electronlove/MiniStudio/Neopixel Board.jpg

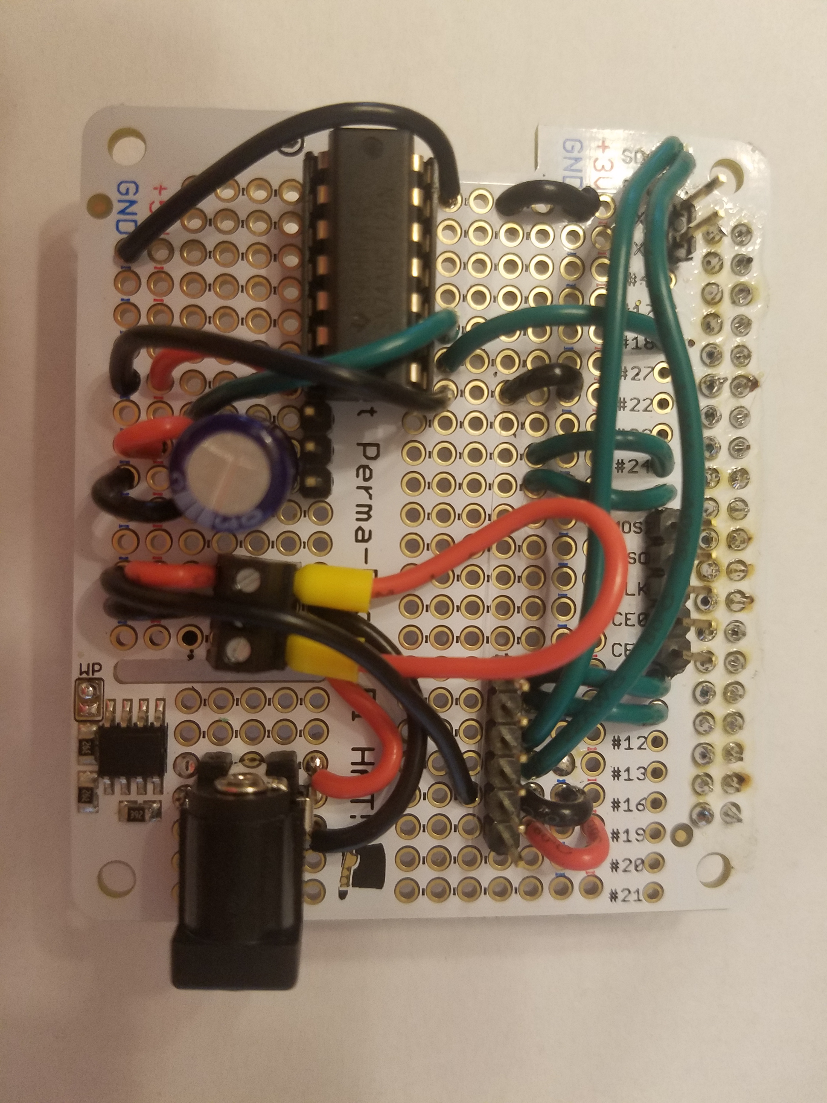
Neopixel Board.jpg
