electronlove/MiniStudio/NeoPixel-Mount.jpg

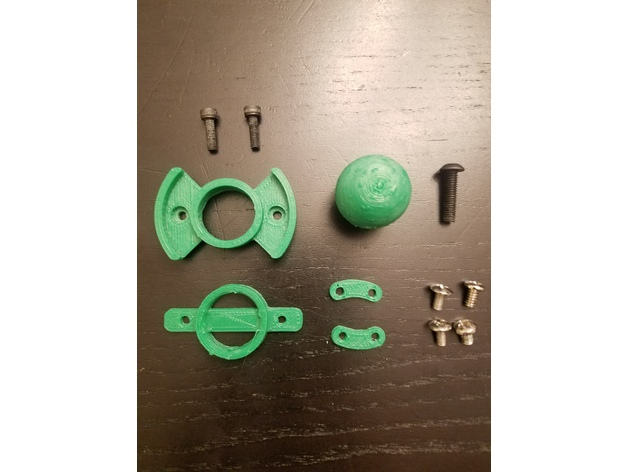
NeoPixel-Mount.jpg
