electronlove/MiniStudio/Snail Box.jpg

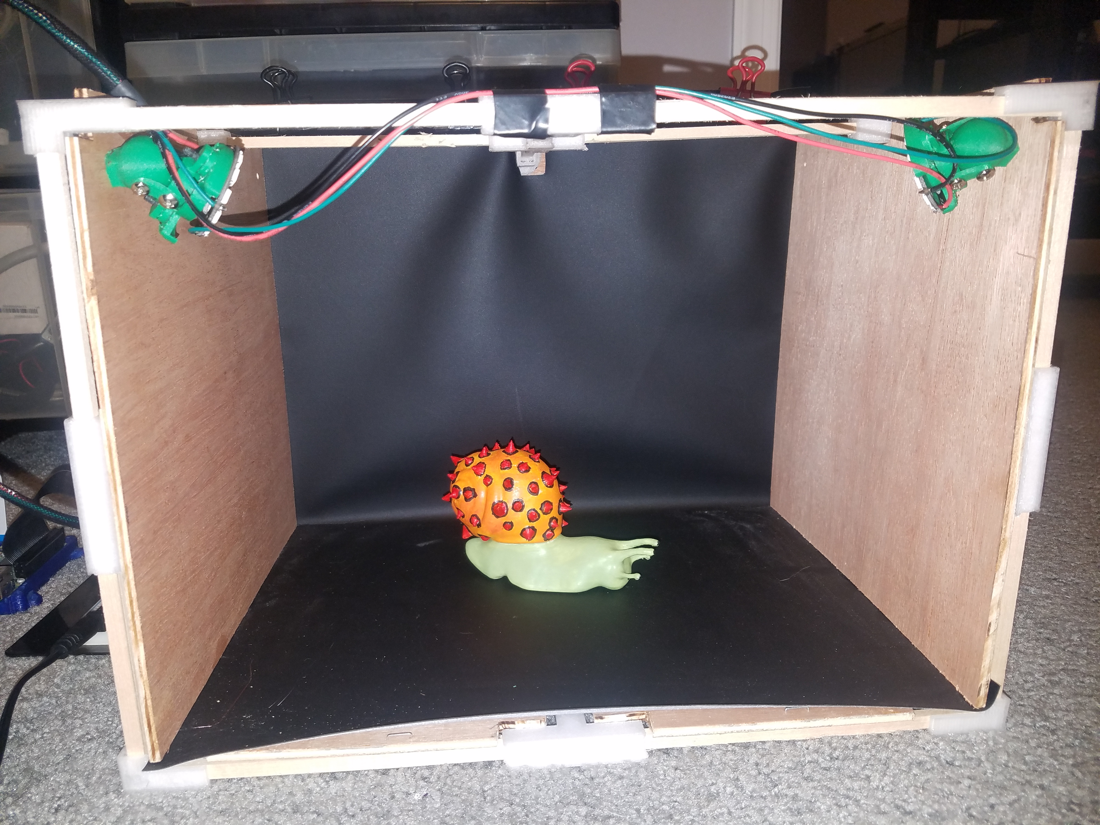
Snail Box.jpg
