electronlove/MiniStudio/STL/LED  with diffuser.jpg

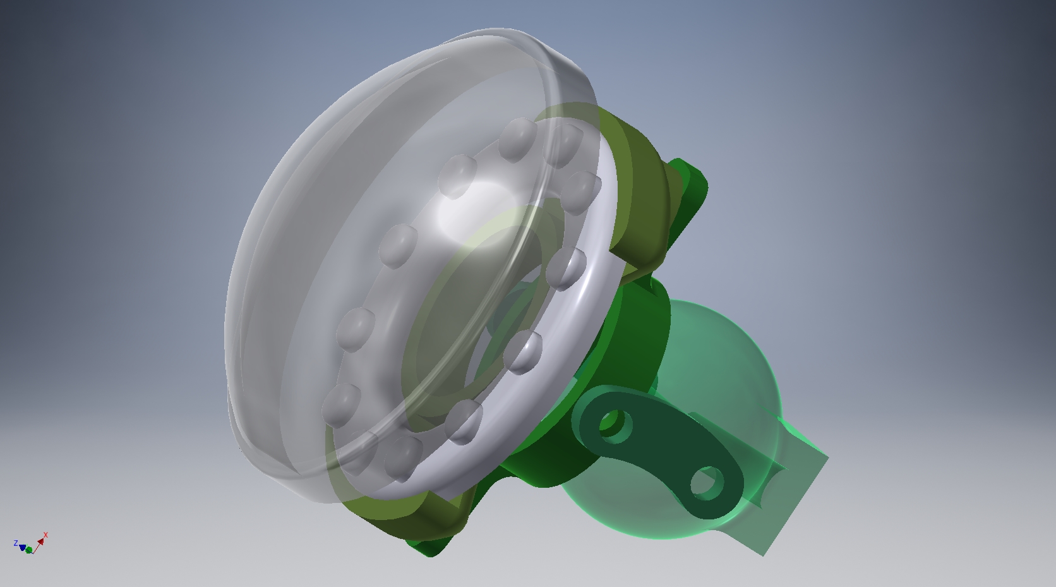
STL/LED with diffuser.jpg
