electronlove/MiniStudio/STL/NeoPixel-render.jpg

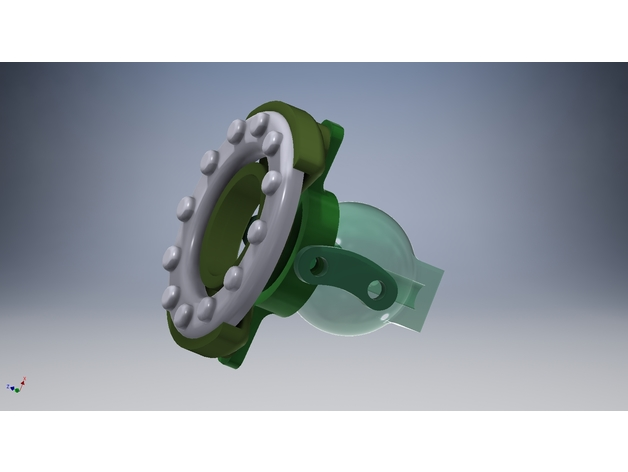
STL/NeoPixel-render.jpg
